mauntrelio/XTCD/scripts/konrad/arm_test.py

import time
import sys
import Adafruit_PCA9685.PCA9685 as pca
pwm = pca (address = 0x41)

pwm.set_pwm_freq(60)
pwm.set_pwm(14,0,400)
time.sleep(1)
pwm.set_pwm(14,0,395)
time.sleep(1)
pwm.set_pwm(14,0,390)
time.sleep(1)
pwm.set_pwm(14,0,385)
time.sleep(1)
pwm.set_pwm(14,0,380)
time.sleep(1)
pwm.set_pwm(14,0,375)
time.sleep(1)
pwm.set_pwm(14,0,370)
time.sleep(1)
pwm.set_pwm(14,0,365)
time.sleep(1)
pwm.set_pwm(14,0,360)
time.sleep(1)
pwm.set_pwm(14,0,355)
time.sleep(1)
pwm.set_pwm(14,0,350)
time.sleep(1)
pwm.set_pwm(14,0,345)
time.sleep(1)
pwm.set_pwm(14,0,340)
time.sleep(1)
pwm.set_pwm(14,0,335)
time.sleep(1)
pwm.set_pwm(14,0,330)
time.sleep(1)
pwm.set_pwm(14,0,325)
time.sleep(1)
pwm.set_pwm(14,0,320)
time.sleep(1)
pwm.set_pwm(14,0,315)
time.sleep(1)
pwm.set_pwm(14,0,310)
time.sleep(1)
